sballano/ergodox_expanse/img/04_teensy_wiring_2.jpg

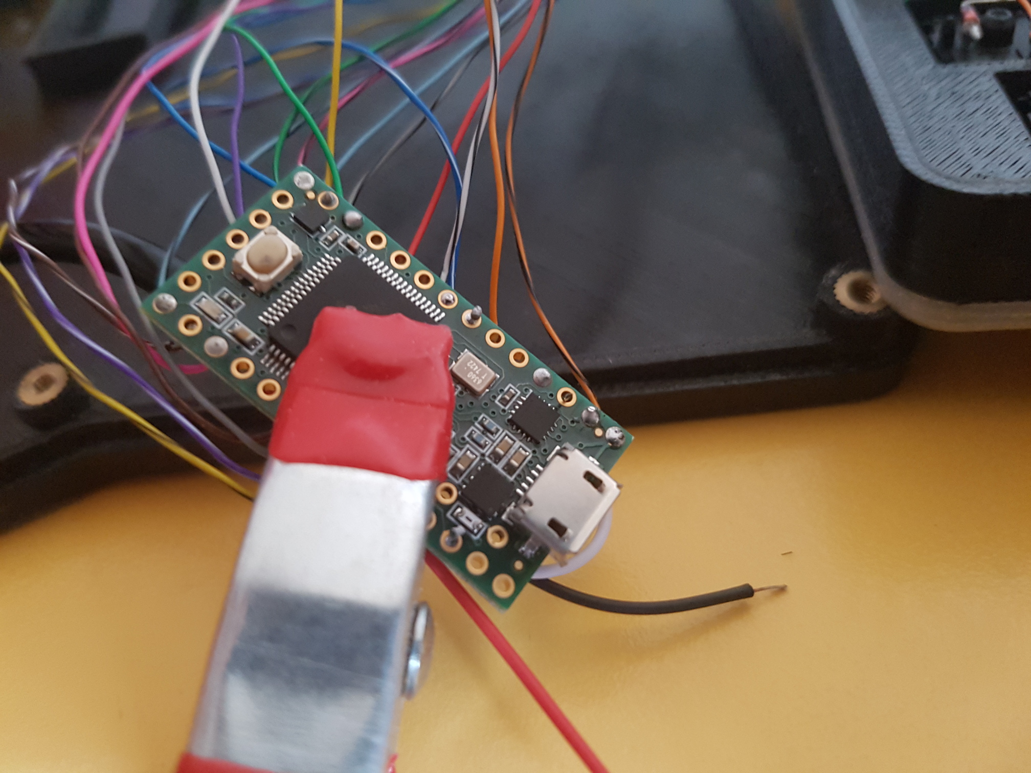
img/04_teensy_wiring_2.jpg
