sballano/ergodox_expanse/img/05_oled_wiring.jpg

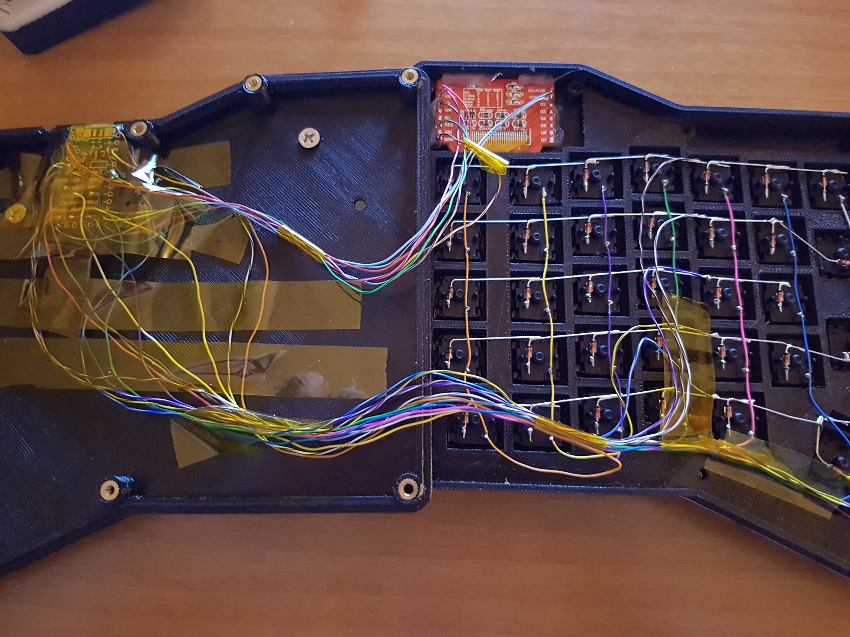
img/05_oled_wiring.jpg
